grigoredy-gif/qfh-weather-satellite-station-/fm_receiver/simulations/sim1c_debug_dc.asc

C1: cap; 65.4p
CE: cap; 47p
D1: diode; DSCH
L1: ind; 2.2u
RE: res; 220k
RP: res; 47k
RS: res; 33k
V1: voltage; SFFM(0 1 12.9Meg {M} 2400)
Named nets: 0, in, tank, audio
.model DSCH D(Is=315n Rs=2.8 N=2.03 Cjo=2.2p Vj=.58 M=.35 Eg=.69 Xti=2)
.step param M list 0 7.083
.tran 0 1m 0 2n
.meas TRAN Vdc AVG V(audio) FROM 0.5833m TO 1m
.meas TRAN Vtankpk MAX V(tank) FROM 0.5833m TO 1m
SIM 1c - debug run: modulated vs unmodulated carrier
Tests: A/B check of the detector with and without FM.
Result: showed that the modulation was not the problem.
Explained in fm_receiver/DESIGN_LOG.md, section 'SIM 1 - slope detector'. Old sheet notes: fm_receiver/sim_notes.md.
