grigoredy-gif/qfh-weather-satellite-station-/fm_receiver/simulations/slope_tank_test.asc

C1: cap; 69.2p
L1: ind; 2.2u
R1: res; 22k
R2: res; 22k
V1: voltage; AC 1
Named nets: 0, in, out
.ac lin 2001 11Meg 15Meg
Tank test - 12.9 MHz tank resonance sanity check
Tests: tank resonance and the schematic-generation workflow.
Result: peak -6 dB at 12.9 MHz, Q about 62, phase crosses zero at resonance.
Explained in fm_receiver/DESIGN_LOG.md, table 'Simulation roadmap (LTspice)', row 0. Old sheet notes: fm_receiver/sim_notes.md.
