grigoredy-gif/qfh-weather-satellite-station-/fm_receiver/simulations/sim10_limiter_detector.asc

C1: cap; 66.7p
CE: cap; 47p
D1: diode; DX
D2: diode; DX
D3: diode; DX
D4: diode; DX
DDET: diode; DSCH
L1: ind; 2.2u
RDRV: res; 10k
RE: res; 220k
Rout: res; 100k
RP: res; 47k
RS: res; 33k
V1: voltage; SINE(0 4 {F})
Named nets: 0, lim, tank, audio
.model DSCH D(Is=315n Rs=2.8 N=2.03 Cjo=2.2p Vj=.58 M=.35 Eg=.69 Xti=2)
.model DX D(Is=2.52n Rs=0.568 N=1.752 Cjo=4p M=0.333 Vj=0.7 Bv=100 Ibv=1u Tt=11.5n)
.step param F 12.85Meg 13.05Meg 5k
.tran 0 100u 0 1n
.options plotwinsize=0
.save V(lim) V(tank) V(audio)
.meas TRAN Vdet AVG V(audio) FROM 60u TO 100u
.meas TRAN Vtank MAX V(tank) FROM 60u TO 100u
.meas TRAN Vlimpp PP V(lim) FROM 60u TO 100u
SIM 10 - integration: limiter into detector
Tests: does the detector S-curve survive the real limiter source?
Result: peak still at 12.95 MHz with a 33k coupling resistor, carrier on a 1.96 mV/kHz linear flank.
Explained in fm_receiver/DESIGN_LOG.md, section 'Integration: SIM 10, 11, 12 - where the standalone testbenches lied'. Old sheet notes: fm_receiver/sim_notes.md.
