grigoredy-gif/qfh-weather-satellite-station-/fm_receiver/simulations/sim11_mixer_filter_if.asc

C2f: cap; 69.2p
Cb2: cap; 10n
Cb2i: cap; 100n
Cbyp: cap; 100n
CE1: cap; 10n
CE1i: cap; 100n
Cin: cap; 1n
Clo: cap; 1n
Crf: cap; 1n
Ct1: cap; 68.7p
Ctank: cap; 69.2p
L2a: ind; 0.507u; Rser=0.5
L2b: ind; 0.588u; Rser=0.5
La1: ind; 0.507u
Lb1: ind; 0.588u
Ltank: ind; 2.2u; Rser=1
Q1: npn; QRF
Q1a: npn; QRF
Q1b: npn; QRF
Q2: npn; QRF
Q3: npn; QRF
RB1: res; 33k
RB1i: res; 33k
RB2: res; 12k
RB2i: res; 12k
Rc2a: res; 8.2k
Rc2b: res; 10k
Rd1: res; 10k
RE1: res; 100
RE1i: res; 180
RE2: res; 220
RE2i: res; 330
RLO: res; 10k
RSlo: res; 50
RSrf: res; 50
RT1: res; 15k
RT2: res; 15k
V2: voltage; 5
VLO: voltage; SINE(0 0.4 125Meg)
VRF: voltage; SINE(0 5m {FRF})
Named nets: 0, vcc, rfsrc, brf, vb2n, blo, e23, if, e1b, t2, tap2, b1, vb2, tap1, c1, c1a, es1
.model QRF NPN(IS=1f BF=100 VAF=60 IKF=0.08 RB=10 RE=0.6 RC=5 CJE=1.1p VJE=0.7 MJE=0.33 CJC=0.7p VJC=0.55 MJC=0.33 XCJC=0.6 TF=28p XTF=2 VTF=4 ITF=0.05 TR=0.5n)
K1 L2a L2b 0.999
K2 Ltank L2a 0.011
K3 Ltank L2b 0.011
K4 La1 Lb1 0.999
.step param FRF list 137.9Meg 138.4Meg
.tran 0 12u 0 0.1n
.options plotwinsize=0
.options method=Gear
.four 12.9Meg 5 4 V(b1)
.meas TRAN Vifpp PP V(if) FROM 10u TO 12u
.meas TRAN Vifpp_mid PP V(if) FROM 7u TO 9u
.meas TRAN Vt2pp PP V(t2) FROM 10u TO 12u
.meas TRAN Vb1pp PP V(b1) FROM 10u TO 12u
.meas TRAN Vtap1pp PP V(tap1) FROM 10u TO 12u
.meas TRAN Ve23dc AVG V(e23) FROM 10u TO 12u
.meas TRAN Ve1bdc AVG V(e1b) FROM 10u TO 12u
.meas TRAN Vc1adc AVG V(c1a) FROM 10u TO 12u
.meas TRAN Ves1dc AVG V(es1) FROM 10u TO 12u
SIM 11 - integration: mixer into IF filter into first IF stage
Tests: interface gain, in-situ selectivity, tap sizing.
Result: +20.6 dB to the first IF base, -29.6 dB at +/-500 kHz, tap re-sized to 13/27.
Explained in fm_receiver/DESIGN_LOG.md, section 'Integration: SIM 10, 11, 12 - where the standalone testbenches lied'. Old sheet notes: fm_receiver/sim_notes.md.
