grigoredy-gif/qfh-weather-satellite-station-/fm_receiver/simulations/sim12_full_receiver.asc

C1_A: cap; 2.7n
C1_D: cap; 66.7p
C1_O: cap; 82p
C1a_B: cap; 8.2p
C1b_B: cap; 56p
C2_A: cap; 2.2n
C2_O: cap; 180p
C2a_B: cap; 8.2p
C2b_B: cap; 56p
C2f_M: cap; 69.2p
C3_A: cap; 8.2n
C4_A: cap; 1.2n
CADC_A: cap; 2.2n
Cb2_M: cap; 10n
Cb2_S: cap; 100n
CB_O: cap; 10n
Cbot_X: cap; 47p
Cbyp_A: cap; 100n
Cbyp_L: cap; 100n
Cbyp_M: cap; 100n
Cbyp_S: cap; 100n
CC1_A: cap; 1u
Cc1_M: cap; 1n
Cc2_S: cap; 1n
Cc3_S: cap; 1n
Cc4_S: cap; 1n
CC_X: cap; 1n
CE1_M: cap; 10n
CE1i_M: cap; 100n
CE2_L: cap; 100n
CE2_O: cap; 100n
CE2_S: cap; 100n
CE3_S: cap; 100n
CE4_A: cap; 100u
CE4_S: cap; 100n
CE_D: cap; 47p
Cf_L: cap; 1n
Cin_L: cap; 1n
Cin_M: cap; 1n
Clo_M: cap; 1n
CM_O: cap; 20f
Cout_L: cap; 1n
CP_O: cap; 5p
Crf_M: cap; 1n
CSUP_A: cap; 100u
Ct1_B: cap; 8.7p
Ct1_M: cap; 68.7p
Ct2_B: cap; 8.7p
Ct2_S: cap; 68.7p
CT2_X: cap; 14p
Ct3_S: cap; 68.7p
Ct4_S: cap; 68.7p
CT_X: cap; 10.8p
Ctank_M: cap; 69.2p
D1_S: diode; DX
D2_S: diode; DX
D3_S: diode; DX
D4_S: diode; DX
DDET_D: diode; DSCH
L1_B: ind; 82n; Rser=0.47
L1_D: ind; 2.2u
L1_X: ind; 150n
L2_B: ind; 82n; Rser=0.47
L2_X: ind; 150n
L2a_M: ind; 0.507u; Rser=0.5
L2b_M: ind; 0.588u; Rser=0.5
L4_S: ind; 2.2u
La1_M: ind; 0.507u
La2_S: ind; 0.507u
La3_S: ind; 0.507u
Lb1_M: ind; 0.588u
Lb2_S: ind; 0.588u
Lb3_S: ind; 0.588u
LM_O: ind; 2.0265m
Ltank_M: ind; 2.2u; Rser=1
Q1_L: npn; QRF
Q1_M: npn; QRF
Q1_O: npn; QRF
Q1_X: npn; QRF
Q1a_A: pnp; QP
Q1a_M: npn; QRF
Q1b_A: pnp; QP
Q1b_M: npn; QRF
Q2_A: npn; QN
Q2_M: npn; QRF
Q2_O: npn; QRF
Q2a_S: npn; QRF
Q2b_S: npn; QRF
Q3_A: pnp; QP
Q3_M: npn; QRF
Q3a_S: npn; QRF
Q3b_S: npn; QRF
Q4_A: npn; QN
Q4a_S: npn; QRF
Q4b_S: npn; QRF
R1_O: res; 9.1k
R2_O: res; 10k
R3_O: res; 11k
R4_O: res; 5.1k
RA1_A: res; 10k
RA2_A: res; 7.5k
RB1_A: res; 10k
RB1_L: res; 820
RB1_M: res; 27k
RB1i_M: res; 27k
RB2_A: res; 7.5k
RB2_L: res; 560
RB2_M: res; 11k
RB2i_M: res; 11k
RB3_S: res; 27k
RB4_A: res; 1k
RB4_S: res; 11k
RB5_S: res; 27k
RB6_S: res; 11k
RB7_S: res; 27k
RB8_S: res; 11k
RB_X: res; 10k
Rc2a_S: res; 6.8k
Rc2b_S: res; 10k
RC4_A: res; 3.3k
RC_L: res; 120
RC_O: res; 330
RD1_A: res; 10k
Rd1_M: res; 10k
RD2_A: res; 6.2k
Rd2_S: res; 10k
Rd3_S: res; 10k
Rd4_S: res; 10k
RE1_A: res; 10k
RE1_L: res; 2.2
RE1_M: res; 100
RE1_O: res; 47
RE1i_M: res; 180
RE2_A: res; 4.7k
RE2_L: res; 47
RE2_M: res; 220
RE2_O: res; 68
RE2i_M: res; 330
RE3_A: res; 10k
RE3_S: res; 180
RE4_S: res; 330
RE4A_A: res; 270
RE4B_A: res; 820
RE5_S: res; 180
RE6_S: res; 330
RE7_S: res; 180
RE8_S: res; 330
RE_D: res; 220k
RE_O: res; 560
Rf_L: res; 470
RLO_M: res; 10k
Rout_S: res; 100k
RP2_X: res; 6.8k
RP_D: res; 47k
RP_X: res; 2.2k
RS_B: res; 50
RS_D: res; 33k
RSUP_A: res; 100
RSX_O: res; 15
RT1_M: res; 13k
RT2_M: res; 15k
V1_B: voltage; AC 1
V2_S: voltage; 4.6
V3_A: voltage; 3.3
Named nets: 0, ant, tapA, bt1, bt2, tapB, n_rf1, vcc, ln_b, ln_c, n_rf2, ln_e, brf, vb2n, blo, e23, if, e1b, ft2, ftap2, b1, vb2, tap1, c1, c1a, es1, n_t1, n_lo, b2, st2, c2, c2a, e2, e2b, b3, st3, c3, c3a, e3, e3b, b4, c4, c4a, e4, e4b, out, n1, n2, dtank, audio, a_b1, ef1, vaud, x1, y1, ef2, x2, y2, ef3, y4, a_ce, a_e4b, adcref, adc, osc, o_b, bb, bufc, xbase, xtank1, lo
.model QRF NPN(IS=1f BF=100 VAF=60 IKF=0.08 RB=10 RE=0.6 RC=5 CJE=1.1p VJE=0.7 MJE=0.33 CJC=0.7p VJC=0.55 MJC=0.33 XCJC=0.6 TF=28p XTF=2 VTF=4 ITF=0.05 TR=0.5n)
.model DX D(Is=2.52n Rs=0.568 N=1.752 Cjo=4p M=0.333 Vj=0.7 Bv=100 Ibv=1u Tt=11.5n)
.model DSCH D(Is=315n Rs=2.8 N=2.03 Cjo=2.2p Vj=.58 M=.35 Eg=.69 Xti=2)
.model QN NPN(IS=1e-14 BF=200 VAF=100 CJE=8p CJC=4p TF=350p RB=10)
.model QP PNP(IS=1e-14 BF=200 VAF=100 CJE=10p CJC=6p TF=400p RB=10)
K1 L1_B L2_B 0.031
K2 L2a_M L2b_M 0.999
K3 Ltank_M L2a_M 0.011
K4 Ltank_M L2b_M 0.011
K5 La1_M Lb1_M 0.999
K6 La2_S Lb2_S 0.999
K7 La3_S Lb3_S 0.999
K8 L1_X L2_X 0.03
.ic V(o_b)=0   <- oscillator startup kick: swap ; for ! ONLY for TRAN runs. At .op an .ic CLAMPS the node and the oscillator reads dead.
.op
.options plotwinsize=0
.net); just use V(tapB)/V(b2) in any .meas you add.
SIM 12 - the full receiver: design authority, the PCB is built from this netlist (4.6 V rail since Sept 2026)
Tests: every block and bias network together on one rail. Run .op first.
Result: .op matches every block sim, total draw 40.7 mA / 187 mW at 4.6 V.
Explained in fm_receiver/DESIGN_LOG.md ('Integration' and 'The supply rail') and in pcb/README.md. Old sheet notes: fm_receiver/sim_notes.md.
