grigoredy-gif/qfh-weather-satellite-station-/fm_receiver/simulations/sim13_fm_endtoend.asc

C1_A: cap; 2.7n
C1_D: cap; 66.7p
C2_A: cap; 2.2n
C3_A: cap; 8.2n
C4_A: cap; 1.2n
CADC_A: cap; 2.2n
Cb2_S: cap; 100n
Cbyp_A: cap; 100n
Cbyp_S: cap; 100n
CC1_A: cap; 1u
Cc1_S: cap; 1n
Cc2_S: cap; 1n
Cc3_S: cap; 1n
Cc4_S: cap; 1n
CE1_S: cap; 100n
CE2_S: cap; 100n
CE3_S: cap; 100n
CE4_A: cap; 100u
CE4_S: cap; 100n
CE_D: cap; 47p
Cin_S: cap; 1n
CSUP_A: cap; 100u
Ct1_S: cap; 68.7p
Ct2_S: cap; 68.7p
Ct3_S: cap; 68.7p
Ct4_S: cap; 68.7p
D1_S: diode; DX
D2_S: diode; DX
D3_S: diode; DX
D4_S: diode; DX
DDET_D: diode; DSCH
L1_D: ind; 2.2u
L4_S: ind; 2.2u
La1_S: ind; 0.507u
La2_S: ind; 0.507u
La3_S: ind; 0.507u
Lb1_S: ind; 0.588u
Lb2_S: ind; 0.588u
Lb3_S: ind; 0.588u
Q1a_A: pnp; QP
Q1a_S: npn; QRF
Q1b_A: pnp; QP
Q1b_S: npn; QRF
Q2_A: npn; QN
Q2a_S: npn; QRF
Q2b_S: npn; QRF
Q3_A: pnp; QP
Q3a_S: npn; QRF
Q3b_S: npn; QRF
Q4_A: npn; QN
Q4a_S: npn; QRF
Q4b_S: npn; QRF
RA1_A: res; 10k
RA2_A: res; 7.5k
RB1_A: res; 10k
RB1_S: res; 33k
RB2_A: res; 7.5k
RB2_S: res; 12k
RB3_S: res; 33k
RB4_A: res; 1k
RB4_S: res; 12k
RB5_S: res; 33k
RB6_S: res; 12k
RB7_S: res; 33k
RB8_S: res; 12k
Rc2a_S: res; 8.2k
Rc2b_S: res; 10k
RC4_A: res; 3.3k
RD1_A: res; 10k
Rd1_S: res; 10k
RD2_A: res; 6.2k
Rd2_S: res; 10k
Rd3_S: res; 10k
Rd4_S: res; 10k
RE1_A: res; 10k
RE1_S: res; 180
RE2_A: res; 4.7k
RE2_S: res; 330
RE3_A: res; 10k
RE3_S: res; 180
RE4_S: res; 330
RE4A_A: res; 270
RE4B_A: res; 820
RE5_S: res; 180
RE6_S: res; 330
RE7_S: res; 180
RE8_S: res; 330
RE_D: res; 220k
Rout_S: res; 100k
RP_D: res; 47k
RS_D: res; 33k
RS_S: res; 1k
RSUP_A: res; 100
V1_S: voltage; SFFM(0 {A} 12.9Meg 7.083 2400)
V2_S: voltage; 5
V3_A: voltage; 3.3
Named nets: 0, vcc, src, b1, t1, c1, c1a, e1, e1b, vb2, b2, t2, c2, c2a, e2, e2b, b3, t3, c3, c3a, e3, e3b, b4, c4, c4a, e4, e4b, out, n1, n2, dtank, audio, a_b1, ef1, vaud, x1, y1, ef2, x2, y2, ef3, y4, a_ce, a_e4b, adcref, adc
.model QRF NPN(IS=1f BF=100 VAF=60 IKF=0.08 RB=10 RE=0.6 RC=5 CJE=1.1p VJE=0.7 MJE=0.33 CJC=0.7p VJC=0.55 MJC=0.33 XCJC=0.6 TF=28p XTF=2 VTF=4 ITF=0.05 TR=0.5n)
.model DX D(Is=2.52n Rs=0.568 N=1.752 Cjo=4p M=0.333 Vj=0.7 Bv=100 Ibv=1u Tt=11.5n)
.model DSCH D(Is=315n Rs=2.8 N=2.03 Cjo=2.2p Vj=.58 M=.35 Eg=.69 Xti=2)
.model QN NPN(IS=1e-14 BF=200 VAF=100 CJE=8p CJC=4p TF=350p RB=10)
.model QP PNP(IS=1e-14 BF=200 VAF=100 CJE=10p CJC=6p TF=400p RB=10)
K1 La1_S Lb1_S 0.999
K2 La2_S Lb2_S 0.999
K3 La3_S Lb3_S 0.999
.step param A list 100u 1m
.ic V(audio)=0.31
.ic V(adc)=1.263
.tran 0 2m 0 1n
.options plotwinsize=0
.save V(b1) V(out) V(dtank) V(audio) V(a_ce) V(adc)
.meas TRAN Vb1pp PP V(b1) FROM 1m TO 1.002m
.meas TRAN Voutpp PP V(out) FROM 1m TO 1.002m
.meas TRAN Vaudiopp PP V(audio) FROM 1.167m TO 2m
.meas TRAN Vauddc AVG V(audio) FROM 1.167m TO 2m
.meas TRAN Vadcpp PP V(adc) FROM 1.167m TO 2m
.meas TRAN Vadcpp_mid PP V(adc) FROM 0.333m TO 1.167m
.meas TRAN Vadcavg AVG V(adc) FROM 1.167m TO 2m
.four 2400 5 2 V(adc)
SIM 13 - FM in, audio out (end to end)
Tests: a true APT FM signal through the IF chain, limiter, detector, audio chain and ADC.
Result (RE4A = 270 ohm): THD 1.10 / 1.82 %, 0.45 / 0.42 Vpp at the ADC.
Explained in fm_receiver/DESIGN_LOG.md, section 'SIM 13 - the money shot: FM in, audio out'. Old sheet notes: fm_receiver/sim_notes.md.
