grigoredy-gif/qfh-weather-satellite-station-/fm_receiver/simulations/sim1a_slope_scurve.asc

C1: cap; 66.7p
CE: cap; 47p
D1: diode; DSCH
L1: ind; 2.2u
RE: res; 220k
RP: res; 47k
RS: res; 33k
V1: voltage; SINE(0 1 {F})
Named nets: 0, in, tank, audio
.model DSCH D(Is=315n Rs=2.8 N=2.03 Cjo=2.2p Vj=.58 M=.35 Eg=.69 Xti=2)
.step param F 12.85Meg 13.05Meg 5k
.tran 0 100u 0 1n
.meas TRAN Vdet AVG V(audio) FROM 60u TO 100u
.meas TRAN Vtank MAX V(tank) FROM 60u TO 100u
.options plotwinsize=0
.save V(tank) V(audio)
SIM 1a - slope detector S-curve (rev 5)
Tests: detector S-curve, optimum detune, linearity window.
Result: peak 520.9 mV at 12.95 MHz, carrier at 83 % of peak.
Explained in fm_receiver/DESIGN_LOG.md, section 'SIM 1 - slope detector'. Old sheet notes: fm_receiver/sim_notes.md.
