grigoredy-gif/qfh-weather-satellite-station-/fm_receiver/simulations/sim1b_slope_demod.asc

C1: cap; 66.7p
CE: cap; 47p
D1: diode; DSCH
L1: ind; 2.2u
RE: res; 220k
RP: res; 47k
RS: res; 33k
V1: voltage; SFFM(0 1 12.9Meg 7.083 2400)
Named nets: 0, in, tank, audio
.model DSCH D(Is=315n Rs=2.8 N=2.03 Cjo=2.2p Vj=.58 M=.35 Eg=.69 Xti=2)
.tran 0 2m 0 1n
.four 2400 9 4 V(audio)
.options plotwinsize=0
.save V(audio) V(tank)
SIM 1b - slope detector FM demodulation (rev 4)
Tests: FM to audio demodulation, recovered level and THD.
Result: about 60 mVpp of 2400 Hz, in-band THD 0.78 %.
Explained in fm_receiver/DESIGN_LOG.md, section 'SIM 1 - slope detector'. Old sheet notes: fm_receiver/sim_notes.md.
