grigoredy-gif/qfh-weather-satellite-station-/fm_receiver/simulations/sim1d_timestep_check.asc

C1: cap; 65.4p
CE: cap; 47p
D1: diode; DSCH
L1: ind; 2.2u
RE: res; 220k
RP: res; 47k
RS: res; 33k
V1: voltage; SINE(0 1 12.9Meg)
Named nets: 0, in, tank, audio
.model DSCH D(Is=315n Rs=2.8 N=2.03 Cjo=2.2p Vj=.58 M=.35 Eg=.69 Xti=2)
.options plotwinsize=0
.tran 0 200u 0 0.5n
.meas TRAN Vdc AVG V(audio) FROM 120u TO 200u
.meas TRAN Vtankpk MAX V(tank) FROM 120u TO 200u
.meas TRAN Idavg AVG I(D1) FROM 120u TO 200u
.meas TRAN Idrms RMS I(D1) FROM 120u TO 200u
SIM 1d - solver timestep check
Tests: timestep convergence, 5n / 2n / 1n / 0.5n ladder.
Result: 1 ns adopted as the standard step.
Explained in fm_receiver/DESIGN_LOG.md, section 'SIM 1 - slope detector'. Old sheet notes: fm_receiver/sim_notes.md.
