grigoredy-gif/qfh-weather-satellite-station-/fm_receiver/simulations/sim2a_audio_freq.asc

C1: cap; 2.7n
C2: cap; 2.2n
C3: cap; 8.2n
C4: cap; 1.2n
CADC: cap; 2.2n
Cbyp: cap; 100n
CC1: cap; 1u
CE4: cap; 100u
CSUP: cap; 100u
Q1a: pnp; QP
Q1b: pnp; QP
Q2: npn; QN
Q3: pnp; QP
Q4: npn; QN
RA1: res; 10k
RA2: res; 7.5k
RB1: res; 10k
RB2: res; 7.5k
RB4: res; 1k
RC4: res; 3.3k
RD1: res; 10k
RD2: res; 6.2k
RE1: res; 10k
RE2: res; 4.7k
RE3: res; 10k
RE4A: res; 150
RE4B: res; 820
RS: res; 150k
RSUP: res; 100
V1: voltage; SINE(0.31 0.06 2400) AC 1
V2: voltage; 5
V3: voltage; 3.3
Named nets: 0, src, in, b1, ef1, vaud, x1, y1, ef2, x2, y2, ef3, y4, ce, e4b, adcref, adc, vcc
.model QN NPN(IS=1e-14 BF=200 VAF=100 CJE=8p CJC=4p TF=350p RB=10)
.model QP PNP(IS=1e-14 BF=200 VAF=100 CJE=10p CJC=6p TF=400p RB=10)
.ac dec 200 10 100Meg
.options plotwinsize=0
.meas AC Gmid FIND mag(V(adc)) AT 2400
.meas AC G400 FIND mag(V(adc)) AT 400
.meas AC G4k4 FIND mag(V(adc)) AT 4400
.meas AC G22k FIND mag(V(adc)) AT 22000
.meas AC G12M9 FIND mag(V(adc)) AT 12.9Meg
SIM 2a - audio low-pass filter (rev 3b)
Tests: anti-alias filter shape ahead of the ESP32 ADC.
Result: passband flat to 0.70 dB, 45.7 dB down at 22 kHz, 171 dB down at the IF.
Explained in fm_receiver/DESIGN_LOG.md, section 'SIM 2 - audio filter and ADC scaling'. Old sheet notes: fm_receiver/sim_notes.md.
