grigoredy-gif/qfh-weather-satellite-station-/fm_receiver/simulations/sim2b_audio_thd.asc

C1: cap; 2.7n
C2: cap; 2.2n
C3: cap; 8.2n
C4: cap; 1.2n
CADC: cap; 2.2n
Cbyp: cap; 100n
CC1: cap; 1u
CE4: cap; 100u
CSUP: cap; 100u
Q1a: pnp; QP
Q1b: pnp; QP
Q2: npn; QN
Q3: pnp; QP
Q4: npn; QN
RA1: res; 10k
RA2: res; 7.5k
RB1: res; 10k
RB2: res; 7.5k
RB4: res; 1k
RC4: res; 3.3k
RD1: res; 10k
RD2: res; 6.2k
RE1: res; 10k
RE2: res; 4.7k
RE3: res; 10k
RE4A: res; 150
RE4B: res; 820
RS: res; 150k
RSUP: res; 100
V1: voltage; SINE(0.31 0.06 2400)
V2: voltage; 5
V3: voltage; 3.3
Named nets: 0, src, in, b1, ef1, vaud, x1, y1, ef2, x2, y2, ef3, y4, ce, e4b, adcref, adc, vcc
.model QN NPN(IS=1e-14 BF=200 VAF=100 CJE=8p CJC=4p TF=350p RB=10)
.model QP PNP(IS=1e-14 BF=200 VAF=100 CJE=10p CJC=6p TF=400p RB=10)
.tran 0 20m 0 1u
.options plotwinsize=0
.four 2400 9 8 V(adc)
.meas TRAN Vadcpp PP V(adc) FROM 10m TO 20m
.meas TRAN Vadcavg AVG V(adc) FROM 10m TO 20m
.meas TRAN Vcedc AVG V(ce) FROM 10m TO 20m
.meas TRAN Vef1dc AVG V(ef1) FROM 10m TO 20m
.meas TRAN Vef2dc AVG V(ef2) FROM 10m TO 20m
.meas TRAN Vef3dc AVG V(ef3) FROM 10m TO 20m
.meas TRAN Vindc AVG V(in) FROM 10m TO 20m
SIM 2b - audio levels, bias and ESP32 interface (rev 3b)
Tests: DC ladder, ADC drive, distortion. (The board uses RE4A = 270 ohm since Sept 2026, see SIM 13.)
Result: 1.02 Vpp on 1.26 V, in-band THD 1.6 %.
Explained in fm_receiver/DESIGN_LOG.md, section 'SIM 2 - audio filter and ADC scaling'. Old sheet notes: fm_receiver/sim_notes.md.
