grigoredy-gif/qfh-weather-satellite-station-/fm_receiver/simulations/sim3_if_filter.asc

C1: cap; 69.2p
C2: cap; 69.2p
L1: ind; 2.2u; Rser=1
L2: ind; 2.2u; Rser=1
RL: res; 33k
RS: res; 33k
V1: voltage; AC 1
Named nets: 0, t1, out
K1 L1 L2 {kc}
.step param kc list 0.005 0.011 0.022
.ac lin 4001 11Meg 15Meg
.options plotwinsize=0
.meas AC Vpk MAX mag(V(out))
.meas AC BW trig mag(V(out))=Vpk/sqrt(2) rise=1 targ mag(V(out))=Vpk/sqrt(2) fall=last
.meas AC V129 FIND mag(V(out)) AT 12.9Meg
.meas AC Vm100 FIND mag(V(out)) AT 12.8Meg
.meas AC Vp100 FIND mag(V(out)) AT 13.0Meg
.meas AC Vm500 FIND mag(V(out)) AT 12.4Meg
.meas AC Vp500 FIND mag(V(out)) AT 13.4Meg
.meas AC Vm1M FIND mag(V(out)) AT 11.9Meg
.meas AC Vp1M FIND mag(V(out)) AT 13.9Meg
.meas AC Vt1 FIND mag(V(t1)) AT 12.9Meg
SIM 3 - IF filter at 12.9 MHz
Tests: achievable bandwidth and shape of the double-tuned filter.
Result: 200.5 kHz at critical coupling, -27.9 dB at +/-500 kHz, -39.9 dB at +/-1 MHz.
Explained in fm_receiver/DESIGN_LOG.md, section 'SIM 3 - the IF filter'. Old sheet notes: fm_receiver/sim_notes.md.
