grigoredy-gif/qfh-weather-satellite-station-/fm_receiver/simulations/sim4b_if_limiting.asc

Cb2: cap; 100n
Cbyp: cap; 100n
Cc1: cap; 1n
Cc2: cap; 1n
Cc3: cap; 1n
Cc4: cap; 1n
CE1: cap; 100n
CE2: cap; 100n
CE3: cap; 100n
CE4: cap; 100n
Cin: cap; 1n
Ct1: cap; 68.7p
Ct2: cap; 68.7p
Ct3: cap; 68.7p
Ct4: cap; 68.7p
D1: diode; DX
D2: diode; DX
D3: diode; DX
D4: diode; DX
L4: ind; 2.2u
La1: ind; 0.507u
La2: ind; 0.507u
La3: ind; 0.507u
Lb1: ind; 0.588u
Lb2: ind; 0.588u
Lb3: ind; 0.588u
Q1a: npn; QRF
Q1b: npn; QRF
Q2a: npn; QRF
Q2b: npn; QRF
Q3a: npn; QRF
Q3b: npn; QRF
Q4a: npn; QRF
Q4b: npn; QRF
RB1: res; 33k
RB2: res; 12k
RB3: res; 33k
RB4: res; 12k
RB5: res; 33k
RB6: res; 12k
RB7: res; 33k
RB8: res; 12k
Rc2a: res; 8.2k
Rc2b: res; 10k
Rd1: res; 10k
Rd2: res; 10k
Rd3: res; 10k
Rd4: res; 10k
RE1: res; 180
RE2: res; 330
RE3: res; 180
RE4: res; 330
RE5: res; 180
RE6: res; 330
RE7: res; 180
RE8: res; 330
Rout: res; 100k
RS: res; 1k
V1: voltage; SINE(0 {A} 12.9Meg)
V2: voltage; 5
Named nets: 0, vcc, src, b1, t1, c1, c1a, e1, e1b, vb2, b2, t2, c2, c2a, e2, e2b, b3, t3, c3, c3a, e3, e3b, b4, c4, c4a, e4, e4b, out, n1, n2
.model QRF NPN(IS=1f BF=100 VAF=60 IKF=0.08 RB=10 RE=0.6 RC=5 CJE=1.1p VJE=0.7 MJE=0.33 CJC=0.7p VJC=0.55 MJC=0.33 XCJC=0.6 TF=28p XTF=2 VTF=4 ITF=0.05 TR=0.5n)
.model DX D(Is=2.52n Rs=0.568 N=1.752 Cjo=4p M=0.333 Vj=0.7 Bv=100 Ibv=1u Tt=11.5n)
K1 La1 Lb1 0.999
K2 La2 Lb2 0.999
K3 La3 Lb3 0.999
.step param A list 1u 5u 30u 300u
.tran 0 30u 0 1n
.options plotwinsize=0
.four 12.9Meg 5 4 V(out)
.meas TRAN Voutpp PP V(out) FROM 25u TO 30u
.meas TRAN Voutpp_mid PP V(out) FROM 21u TO 26u
.meas TRAN Vc4pp PP V(c4) FROM 25u TO 30u
.meas TRAN Vb4pp PP V(b4) FROM 25u TO 30u
.meas TRAN Vc1pp PP V(c1) FROM 25u TO 30u
.meas TRAN Ve1dc AVG V(e1) FROM 25u TO 30u
.meas TRAN Ve2dc AVG V(e2) FROM 25u TO 30u
.meas TRAN Ve3dc AVG V(e3) FROM 25u TO 30u
.meas TRAN Ve4dc AVG V(e4) FROM 25u TO 30u
.meas TRAN Vc1adc AVG V(c1a) FROM 25u TO 30u
SIM 4b - IF chain + limiter (rev 3)
Tests: does the output stop following the input?
Result: +20 dB in gives +1.6 dB out, 2.51 Vpp delivered, limiting from about 22 uV.
Explained in fm_receiver/DESIGN_LOG.md, section 'SIM 4 - the IF amplifier and limiter'. Old sheet notes: fm_receiver/sim_notes.md.
