grigoredy-gif/qfh-weather-satellite-station-/fm_receiver/simulations/sim5_multiplier_x5.asc

CC: cap; 1n
CT2: cap; 10.8p
CT: cap; 10.8p
L1: ind; 150n
L2: ind; 150n
Q1: npn; QRF
RB: res; 10k
RP2: res; 6.8k
RP: res; 2.2k
V1: voltage; SINE(0 1 25Meg)
V2: voltage; 5
Named nets: 0, in, base, tank1, lo
.model QRF NPN(IS=1f BF=100 VAF=60 IKF=0.08 RB=10 RE=0.6 RC=5 CJE=1.1p VJE=0.7 MJE=0.33 CJC=0.7p VJC=0.55 MJC=0.33 XCJC=0.6 TF=28p XTF=2 VTF=4 ITF=0.05 TR=0.5n)
K1 L1 L2 0.03
.tran 0 2u 0 0.1n
.options plotwinsize=0
.save V(lo) V(tank1) Ic(Q1)
.four 25Meg 10 4 V(lo)
.meas TRAN Vlopp PP V(lo) FROM 1.5u TO 2u
.meas TRAN Vt1pp PP V(tank1) FROM 1.5u TO 2u
.meas TRAN Icpk MAX Ic(Q1) FROM 1.5u TO 2u
.meas TRAN Icavg AVG Ic(Q1) FROM 1.5u TO 2u
.meas TRAN Vt1min MIN V(tank1) FROM 1.5u TO 2u
SIM 5 - x5 frequency multiplier (rev 4, 5 V)
Tests: 5th-harmonic level, rejection of the 4th and 6th.
Result: topology validated, H4 -36.7 dB, H6 -42.1 dB (for the absolute H5 level see SIM 5b).
Explained in fm_receiver/DESIGN_LOG.md, section 'SIM 5 - x5 frequency multiplier (the LO chain)'. Old sheet notes: fm_receiver/sim_notes.md.
