grigoredy-gif/qfh-weather-satellite-station-/fm_receiver/simulations/sim5b_multiplier_drive.asc

CC: cap; 1n
CT2: cap; 10.8p
CT: cap; 10.8p
L1: ind; 150n
L2: ind; 150n
Q1: npn; QRF
RB: res; 10k
RP2: res; 6.8k
RP: res; 2.2k
RSRC: res; 330
V1: voltage; SINE(0 {A} 25Meg)
V2: voltage; 5
Named nets: 0, in, drv, base, tank1, lo
.model QRF NPN(IS=1f BF=100 VAF=60 IKF=0.08 RB=10 RE=0.6 RC=5 CJE=1.1p VJE=0.7 MJE=0.33 CJC=0.7p VJC=0.55 MJC=0.33 XCJC=0.6 TF=28p XTF=2 VTF=4 ITF=0.05 TR=0.5n)
K1 L1 L2 0.03
.tran 0 40u 0 0.1n
.options plotwinsize=0
.save V(lo) V(tank1) V(drv) Ic(Q1)
.four 25Meg 10 4 V(lo)
.step param A list 0.65 0.75 0.95 1.15
.meas TRAN Vlopp PP V(lo) FROM 35u TO 40u
.meas TRAN Vlopp_mid PP V(lo) FROM 20u TO 25u
.meas TRAN Vdrvpp PP V(drv) FROM 35u TO 40u
.meas TRAN Vt1pp PP V(tank1) FROM 35u TO 40u
.meas TRAN Icpk MAX Ic(Q1) FROM 35u TO 40u
.meas TRAN Icavg AVG Ic(Q1) FROM 35u TO 40u
.meas TRAN Vt1min MIN V(tank1) FROM 35u TO 40u
.step line present, and K1 L1 L2 0.03 still there (no galvanic tank link).
SIM 5b - multiplier drive robustness (rev 3, 5 V)
Tests: settled H5 with a realistic 330 ohm drive.
Result: nominal H5 1.68 V, -20 % corner 1.02 V (3.4x what the mixer needs), no saturation.
Explained in fm_receiver/DESIGN_LOG.md, section 'SIM 5b - multiplier drive robustness'. Old sheet notes: fm_receiver/sim_notes.md.
