grigoredy-gif/qfh-weather-satellite-station-/fm_receiver/simulations/sim6_xtal_oscillator.asc

C1: cap; 82p
C2: cap; 180p
CM: cap; 20f
CP: cap; 5p
LM: ind; 2.0265m
Q1: npn; QRF
R1: res; 11k
R2: res; 10k
RE: res; 560
RSX: res; 15
V2: voltage; 5
Named nets: 0, osc, b
.model QRF NPN(IS=1f BF=100 VAF=60 IKF=0.08 RB=10 RE=0.6 RC=5 CJE=1.1p VJE=0.7 MJE=0.33 CJC=0.7p VJC=0.55 MJC=0.33 XCJC=0.6 TF=28p XTF=2 VTF=4 ITF=0.05 TR=0.5n)
.tran 0 3m 0 2n
.options plotwinsize=0
.save V(osc) V(b)
.ic V(b)=0
.four 25Meg 5 4 V(osc)
.meas TRAN Vpp_early PP V(osc) FROM 200u TO 250u
.meas TRAN Vpp PP V(osc) FROM 2.9m TO 3m
.meas TRAN Vosc_dc AVG V(osc) FROM 2.9m TO 3m
.meas TRAN Vpp_mid PP V(osc) FROM 1.45m TO 1.5m
.four fundamental at 25 MHz dominant. Report Vpp: the x5 multiplier (SIM 5) wants
SIM 6 - 25 MHz crystal oscillator (rev 2, 5 V)
Tests: startup, amplitude limiting, frequency.
Result: starts from the .ic kick, limits at 409.7 mVpp, 25 MHz dominant.
Explained in fm_receiver/DESIGN_LOG.md, section 'SIM 6 - 25 MHz crystal oscillator'. Old sheet notes: fm_receiver/sim_notes.md.
