grigoredy-gif/qfh-weather-satellite-station-/fm_receiver/simulations/sim6b_osc_buffer.asc

C1: cap; 82p
C2: cap; 180p
CB: cap; 10n
CC2: cap; 1n
CE2: cap; 100n
CM: cap; 20f
CP: cap; 5p
LM: ind; 2.0265m
Q1: npn; QRF
Q2: npn; QRF
R1: res; 11k
R2: res; 10k
R3: res; 12k
R4: res; 5.1k
RB2: res; 10k
RC: res; 330
RE1: res; 47
RE2: res; 68
RE: res; 560
RSX: res; 15
V2: voltage; 5
Named nets: 0, osc, b, bb, bufc, drv
.model QRF NPN(IS=1f BF=100 VAF=60 IKF=0.08 RB=10 RE=0.6 RC=5 CJE=1.1p VJE=0.7 MJE=0.33 CJC=0.7p VJC=0.55 MJC=0.33 XCJC=0.6 TF=28p XTF=2 VTF=4 ITF=0.05 TR=0.5n)
.tran 0 3m 0 1n
.options plotwinsize=0
.save V(osc) V(b) V(drv) V(bufc)
.ic V(b)=0
.four 25Meg 5 4 V(osc)
.four 25Meg 5 4 V(drv)
.meas TRAN Vpp_early PP V(osc) FROM 200u TO 250u
.meas TRAN Vpp_osc PP V(osc) FROM 2.9m TO 3m
.meas TRAN Vpp_buf PP V(drv) FROM 2.9m TO 3m
.meas TRAN Vpp_buf_mid PP V(drv) FROM 1.45m TO 1.5m
.meas TRAN Vbufc_dc AVG V(bufc) FROM 2.9m TO 3m
.meas TRAN Vosc_dc AVG V(osc) FROM 2.9m TO 3m
SIM 6b - oscillator buffer / multiplier driver (rev 3, 5 V)
Tests: drive for the multiplier, crystal isolation.
Result: 2.33 Vpp into the replica load, no added clipping, oscillator untouched.
Explained in fm_receiver/DESIGN_LOG.md, section 'SIM 6 - 25 MHz crystal oscillator' (SIM 6b part). Old sheet notes: fm_receiver/sim_notes.md.
