grigoredy-gif/qfh-weather-satellite-station-/fm_receiver/simulations/sim7_input_bpf.asc

C1a: cap; 8.2p
C1b: cap; 56p
C2a: cap; 8.2p
C2b: cap; 56p
Ct1: cap; 8.7p
Ct2: cap; 8.7p
L1: ind; 82n; Rser=0.47
L2: ind; 82n; Rser=0.47
RL: res; 50
RS: res; 50
V1: voltage; AC 1
Named nets: 0, src, tapA, t1, t2, tapB, out
K1 L1 L2 {kc}
.step param kc list 0.015 0.031 0.062
.ac lin 4001 80Meg 200Meg
.options plotwinsize=0
.meas AC Vpk MAX mag(V(out))
.meas AC BW trig mag(V(out))=Vpk/sqrt(2) rise=1 targ mag(V(out))=Vpk/sqrt(2) fall=last
.meas AC V1379 FIND mag(V(out)) AT 137.9Meg
.meas AC V1371 FIND mag(V(out)) AT 137.1Meg
.meas AC Vimage FIND mag(V(out)) AT 112.1Meg
.meas AC Vfm FIND mag(V(out)) AT 108Meg
.meas AC Vair FIND mag(V(out)) AT 118Meg
.meas AC V150 FIND mag(V(out)) AT 150Meg
SIM 7 - input band-pass filter, 50 ohm in and out (rev 2, Sept 2026)
Tests: image rejection at 112.1 MHz, passband, insertion loss.
Result: 39.5 dB image rejection, 6.1 MHz passband, 2.4 dB insertion loss (trimmer ~6.5 pF on the board).
Explained in fm_receiver/DESIGN_LOG.md, section 'SIM 7 - the input filter'. Old sheet notes: fm_receiver/sim_notes.md.
