grigoredy-gif/qfh-weather-satellite-station-/fm_receiver/simulations/sim8_mixer.asc

Cb2: cap; 10n
Cbyp: cap; 100n
CE1: cap; 10n
Clo: cap; 1n
Crf: cap; 1n
Ctank: cap; 69.2p
Ltank: ind; 2.2u; Rser=1
Q1: npn; QRF
Q2: npn; QRF
Q3: npn; QRF
RB1: res; 33k
RB2: res; 12k
RE1: res; 100
RE2: res; 220
RLO: res; 10k
Rp: res; 6.8k
RSlo: res; 50
RSrf: res; 50
RT1: res; 15k
RT2: res; 15k
V2: voltage; 5
VLO: voltage; SINE(0 {ALO} 125Meg)
VRF: voltage; SINE(0 5m {FRF})
Named nets: 0, vcc, rfsrc, brf, vb2n, blo, e23, if, e1b
.model QRF NPN(IS=1f BF=100 VAF=60 IKF=0.08 RB=10 RE=0.6 RC=5 CJE=1.1p VJE=0.7 MJE=0.33 CJC=0.7p VJC=0.55 MJC=0.33 XCJC=0.6 TF=28p XTF=2 VTF=4 ITF=0.05 TR=0.5n)
.step param FRF list 137.9Meg 112.1Meg
.step param ALO list 0.1 0.2 0.4 0.8
.tran 0 6u 0 0.1n
.options plotwinsize=0
.options method=Gear
.four 12.9Meg 5 4 V(if)
.meas TRAN Vifpp PP V(if) FROM 4u TO 6u
.meas TRAN Vifpp_mid PP V(if) FROM 2.5u TO 4.5u
.meas TRAN Ve23dc AVG V(e23) FROM 4u TO 6u
.meas TRAN Ve1bdc AVG V(e1b) FROM 4u TO 6u
SIM 8 - mixer (rev 2, 5 V)
Tests: conversion gain, LO drive plateau, image response.
Result: 22.8 dB conversion gain, flat for LO >= 0.4 V, image within 0.04 dB of the wanted signal.
Explained in fm_receiver/DESIGN_LOG.md, section 'SIM 8 - the mixer'. Old sheet notes: fm_receiver/sim_notes.md.
