grigoredy-gif/qfh-weather-satellite-station-/fm_receiver/simulations/sim9_lna.asc

Cbyp: cap; 100n
CE2: cap; 100n
Cf: cap; 1n
Cin: cap; 1n
Cout: cap; 1n
Q1: npn; QRF
RB1: res; 910
RB2: res; 560
RC: res; 120
RE1: res; 2.2
RE2: res; 47
Rf: res; 470
RL: res; 50
RS: res; 50
V1: voltage; AC 1
V2: voltage; 5
Named nets: 0, vcc, src, in, b, c, out, e
.model QRF NPN(IS=1f BF=100 VAF=60 IKF=0.08 RB=10 RE=0.6 RC=5 CJE=1.1p VJE=0.7 MJE=0.33 CJC=0.7p VJC=0.55 MJC=0.33 XCJC=0.6 TF=28p XTF=2 VTF=4 ITF=0.05 TR=0.5n)
.ac dec 400 10Meg 1000Meg
.options plotwinsize=0
.meas AC G1379 FIND mag(V(out)) AT 137.9Meg
.meas AC Vb1379 FIND mag(V(b)) AT 137.9Meg
.meas AC G20 FIND mag(V(out)) AT 20Meg
.meas AC G300 FIND mag(V(out)) AT 300Meg
.meas AC G700 FIND mag(V(out)) AT 700Meg
.meas AC Gpk MAX mag(V(out))
SIM 9 - LNA (rev 2, 5 V)
Tests: 50 ohm match and gain ahead of the mixer.
Result: S21 15.8 dB, Zin 38 ohm (VSWR 1.31). On the real board expect about 14.1 dB (layout emitter inductance).
Explained in fm_receiver/DESIGN_LOG.md, section 'SIM 9 - the LNA'. Old sheet notes: fm_receiver/sim_notes.md.
